rvgimst/Mandalorian-helmet/pics/2085_standby-symbol.png

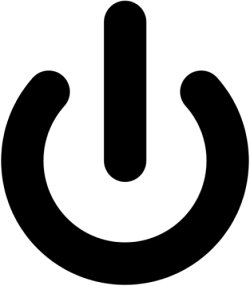
pics/2085_standby-symbol.png
