rvgimst/Mandalorian-helmet/pics/istockphoto-speakergrill.jpg

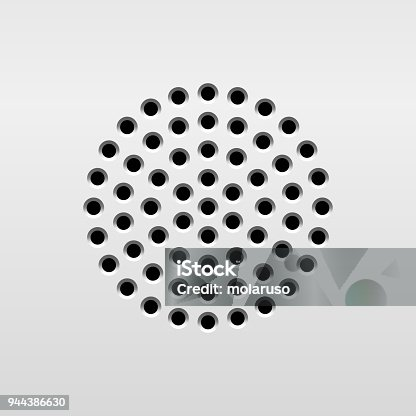
pics/istockphoto-speakergrill.jpg
