rvgimst/Mandalorian-helmet/pics/lamp on1.png

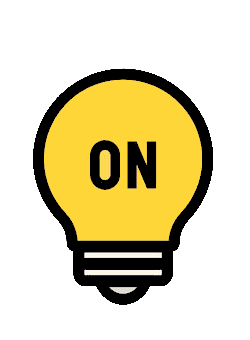
pics/lamp on1.png
