rvgimst/Mandalorian-helmet/pics/lamp on-off.jpeg

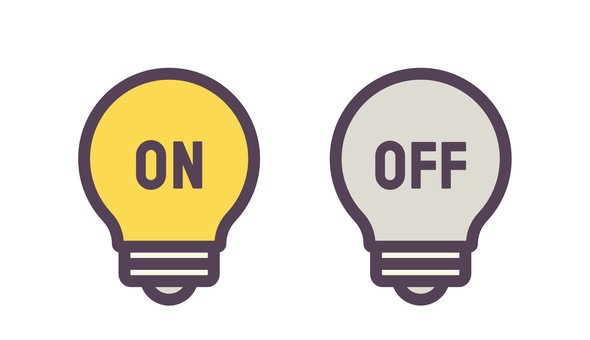
pics/lamp on-off.jpeg
