rvgimst/Mandalorian-helmet/pics/mando helmet front.png

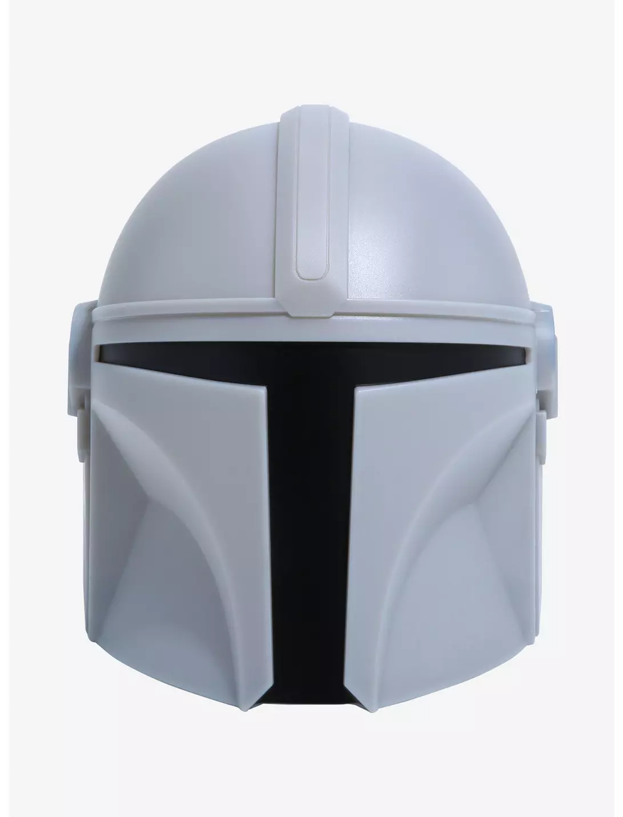
pics/mando helmet front.png
