rvgimst/Mandalorian-helmet/pics/music.jpg

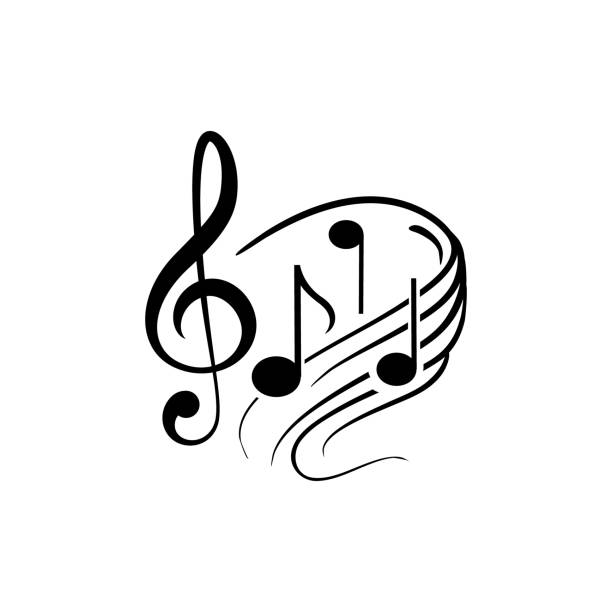
pics/music.jpg
