rvgimst/Mandalorian-helmet/pics/push button.png

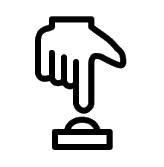
pics/push button.png
