rvgimst/Mandalorian-helmet/pics/speaker-grill_098.png

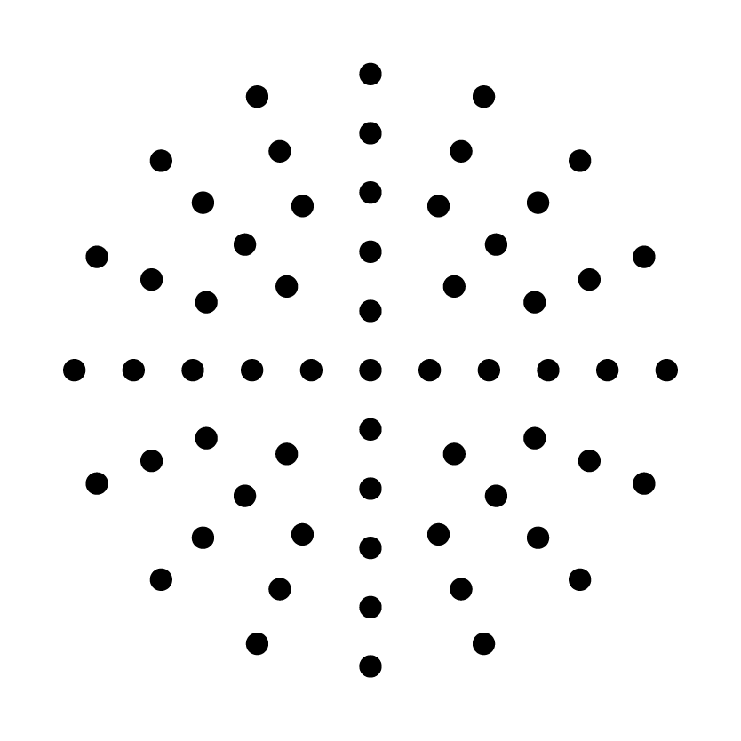
pics/speaker-grill_098.png
